javiser/crescendo-clock/hardware/pictures/display_pins_soldering.jpg

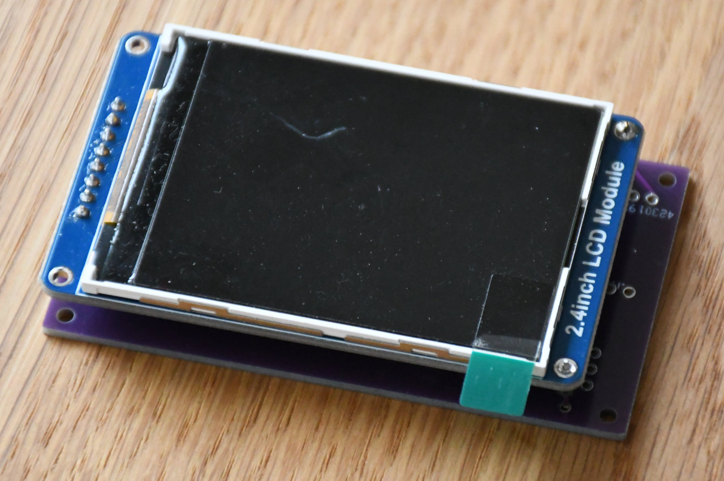
hardware/pictures/display_pins_soldering.jpg
