javiser/crescendo-clock/src/Antonio_Regular26pt7b.h

const uint8_t Antonio_Regular26pt7bBitmaps[] PROGMEM = {
  0x00, 0xFF, 0xFF, 0xFF, 0xFF, 0xFF, 0xFF, 0xFF, 0xFC, 0x00, 0x07, 0xC0,
  0x00, 0x7C, 0xE0, 0x67, 0xCE, 0x06, 0x7C, 0xE0, 0x67, 0xCF, 0x06, 0x7C,
  0xF0, 0x67, 0xCF, 0x06, 0x7C, 0xF0, 0x67, 0xCF, 0x86, 0x7C, 0xF8, 0x67,
  0xCF, 0x86, 0x7C, 0xF8, 0x67, 0xCF, 0xC6, 0x7C, 0xFC, 0x67, 0xCE, 0xC6,
  0x7C, 0xEE, 0x67, 0xCE, 0xE6, 0x7C, 0xEE, 0x67, 0xCE, 0x66, 0x7C, 0xE7,
  0x67, 0xCE, 0x76, 0x7C, 0xE3, 0x67, 0xCE, 0x36, 0x7C, 0xE3, 0xE7, 0xCE,
  0x3E, 0x7C, 0xE1, 0xE7, 0xCE, 0x1E, 0x7C, 0xE1, 0xE7, 0xCE, 0x1E, 0x7C,
  0xE0, 0xE7, 0xCE, 0x0E, 0x7C, 0xE0, 0xE7, 0xCE, 0x0E, 0x7C, 0xE0, 0x67,
  0xCE, 0x06, 0x7C, 0x00, 0x07, 0xC0, 0x00, 0x7F, 0xFF, 0xFF, 0xFF, 0xFF,
  0xFF, 0xFF, 0xFF, 0xFF, 0xFF, 0xFF, 0xFF, 0xFF, 0xFF, 0xFF, 0xFC, 0x00,
  0x07, 0xC0, 0x00, 0x7C, 0xE0, 0x67, 0xCE, 0x06, 0x7C, 0xE0, 0x67, 0xCF,
  0x06, 0x7C, 0xF0, 0x67, 0xCF, 0x06, 0x7C, 0xF0, 0x67, 0xCF, 0x86, 0x7C,
  0xF8, 0x67, 0xCF, 0x86, 0x7C, 0xF8, 0x67, 0xCF, 0xC6, 0x7C, 0xFC, 0x67,
  0xCE, 0xC6, 0x7C, 0xEE, 0x67, 0xCE, 0xE6, 0x7C, 0xEE, 0x67, 0xCE, 0x66,
  0x7C, 0xE7, 0x67, 0xCE, 0x76, 0x7C, 0xE3, 0x67, 0xCE, 0x36, 0x7C, 0xE3,
  0xE7, 0xCE, 0x3E, 0x7C, 0xE1, 0xE7, 0xCE, 0x1E, 0x7C, 0xE1, 0xE7, 0xCE,
  0x1E, 0x7C, 0xE0, 0xE7, 0xCE, 0x0E, 0x7C, 0xE0, 0xE7, 0xCE, 0x0E, 0x7C,
  0xE0, 0x67, 0xCE, 0x06, 0x7C, 0x00, 0x07, 0xC0, 0x00, 0x7F, 0xFF, 0xFF,
  0xFF, 0xFF, 0xFF, 0xFF, 0xFF, 0xFF, 0xFF, 0xFF, 0xFF, 0xFF, 0xFF, 0xFF,
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
  {  3398,  23,  23,  21,   -1,  -30 },   // 0x45 'E'
  {  3465,  29,  27,  21,   -3,  -30 } }; // 0x46 'F'

const GFXfont Antonio_Regular26pt7b PROGMEM = {
  (uint8_t  *)Antonio_Regular26pt7bBitmaps,
  (GFXglyph *)Antonio_Regular26pt7bGlyphs,
  0x20, 0x46, 66 };

// Approx. 3843 bytes
