javiser/crescendo-clock/src/Antonio_Light16pt7b.h

const uint8_t Antonio_Light16pt7bBitmaps[] PROGMEM = {
  0xFF, 0xFF, 0xE0, 0xE0, 0xE0, 0xE0, 0xE0, 0xE0, 0xE0, 0xE0, 0xE0, 0xE0,
  0xFF, 0xFF, 0xE0, 0xE0, 0xE0, 0xE0, 0xE0, 0xE0, 0xE0, 0xE0, 0xE0, 0xE0,
  0xE0, 0xFF, 0xFF, 0xFF, 0xFF, 0xE0, 0xE0, 0xE0, 0xE0, 0xE0, 0xE0, 0xE0,
  0xE0, 0xE0, 0xFF, 0xFF, 0xFF, 0xE0, 0xE0, 0xE0, 0xE0, 0xE0, 0xE0, 0xE0,
  0xE0, 0xE0, 0xE0, 0xE0, 0xE0, 0xE0, 0x3F, 0x1F, 0xE7, 0x3B, 0x87, 0xE1,
  0xF8, 0x7E, 0x1F, 0x87, 0xE1, 0xF8, 0x7E, 0x03, 0x80, 0xE0, 0x39, 0xFE,
  0x7F, 0x87, 0xE1, 0xF8, 0x7E, 0x1F, 0x87, 0xE1, 0xF8, 0x7E, 0x1F, 0x87,
  0x73, 0xDF, 0xF3, 0xEC, 0xE0, 0xF8, 0x3E, 0x0F, 0x83, 0xE0, 0xF8, 0x3E,
  0x0F, 0x83, 0xE0, 0xF8, 0x3E, 0x0F, 0x83, 0xFF, 0xFF, 0xFE, 0x0F, 0x83,
  0xE0, 0xF8, 0x3E, 0x0F, 0x83, 0xE0, 0xF8, 0x3E, 0x0F, 0x83, 0xE0, 0xF8,
  0x3E, 0x0C, 0xFF, 0xFF, 0xFF, 0xFF, 0xFF, 0xFF, 0xFF, 0xFF, 0xFF, 0xFF,
  0x80, 0x01, 0x80, 0xC0, 0x60, 0x30, 0x18, 0x0C, 0x06, 0x03, 0x01, 0x80,
  0xC0, 0x60, 0x30, 0x18, 0x0C, 0x06, 0x03, 0x01, 0x80, 0xF8, 0x7C, 0x3E,
  0x1F, 0x0F, 0x87, 0xC7, 0x73, 0xBF, 0x8F, 0xC0, 0xE0, 0xFC, 0x1B, 0x87,
  0x70, 0xEE, 0x39, 0xC7, 0x38, 0xC7, 0x38, 0xE7, 0x1C, 0xC3, 0xB8, 0x76,
  0x0F, 0xC1, 0xF8, 0x3F, 0x07, 0x70, 0xEE, 0x1C, 0xC3, 0x9C, 0x73, 0x8E,
  0x39, 0xC7, 0x38, 0x67, 0x0E, 0xE1, 0xDC, 0x1F, 0x83, 0x80, 0xE0, 0xE0,
  0xE0, 0xE0, 0xE0, 0xE0, 0xE0, 0xE0, 0xE0, 0xE0, 0xE0, 0xE0, 0xE0, 0xE0,
  0xE0, 0xE0, 0xE0, 0xE0, 0xE0, 0xE0, 0xE0, 0xE0, 0xE0, 0xE0, 0xE0, 0xFF,
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
  {   563,  12,  27,  13,    1,  -26 },   // 0x56 'V'
  {   604,  18,  27,  20,    1,  -26 } }; // 0x57 'W'

const GFXfont Antonio_Light16pt7b PROGMEM = {
  (uint8_t  *)Antonio_Light16pt7bBitmaps,
  (GFXglyph *)Antonio_Light16pt7bGlyphs,
  0x45, 0x57, 41 };

// Approx. 805 bytes
